Than0s-baba/Analogverse-26/Phase1/Draft1 (2).asc

C1: cap; 1µ
C2: cap; 1µ
C3: cap; 1µ
C4: cap; 1µ
C5: cap; 1µ
C6: cap; 1µ
C7: cap; 2µ
C8: cap; 1µ
C9: cap; 1µ
C10: cap; 0.125µ
C11: cap; 0.125µ
C12: cap; 1µ
C13: cap; 1µ
C14: cap; 1µ
C15: cap; 1µ
C16: cap; 2µ
R1: res; 10k
R2: res; 10k
R3: res; 20k
R4: res; 27k
R5: res; 27k
R6: res; 11k
R7: res; 11k
R8: res; 10k
R9: res; 10k
R10: res; 9.9k
R11: res; 0.1k
R12: res; 3.3k
R13: res; 3.3k
R14: res; 1.6k
R15: res; 10k
R16: res; 10k
R17: res; 11k
R18: res; 11k
R19: res; 2k
R20: res; 1k
R21: res; 1k
R22: res; 1k
R23: res; 0.85k
R24: res; 10k
R25: res; 10k
R26: res; 27k
R27: res; 27k
R28: res; 10k
R29: res; 10k
R30: res; 3.3k
R31: res; 3.3k
R32: res; 1.6k
R33: res; 10k
R34: res; 10k
R: res; 10k
Rg: res; 5k
RR: res; 20k
rrr: res; 10
U1: LT1001
U2: LT1001
U3: LT1001
U4: LT1001
U5: LT1001
U6: LT1001
U9: LT1001
U10: LT1001
U11: LT1001
U12: LT1001
U13: LT1001
U15: LT1001
U16: LT1001
V1: voltage; 5
V2: voltage; 5
V3: voltage; 5
V4: voltage; 5
V5: voltage; 5
V8: voltage; SINE(0 50u 10)
Vreference: voltage; SINE(200m 500m 50)
Named nets: 0
Vreference
Vactive
High pass filter
instrumental amplifier
Low pass filter
Notch filter
.tran 0 2 0 1m
+5v
-5v
High pass filter
